Pasq104/SWDP-GeoGuesserProject/Report/img/ble_config2.png

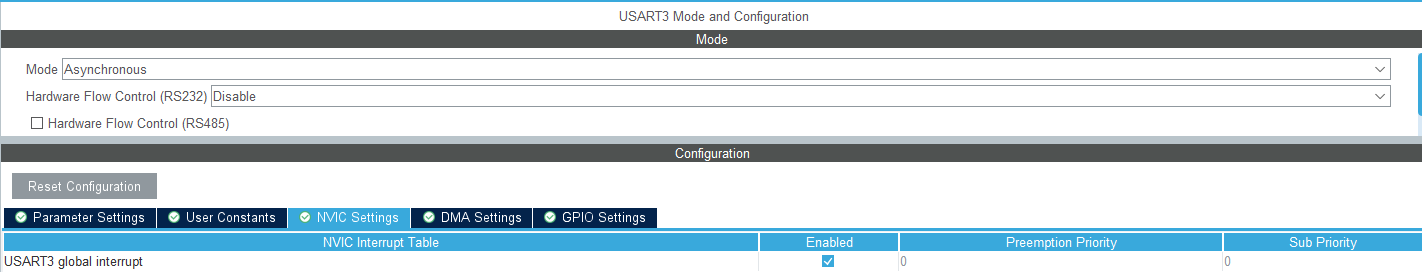
Report/img/ble_config2.png
