Pasq104/SWDP-GeoGuesserProject/Report/img/ble_config.png

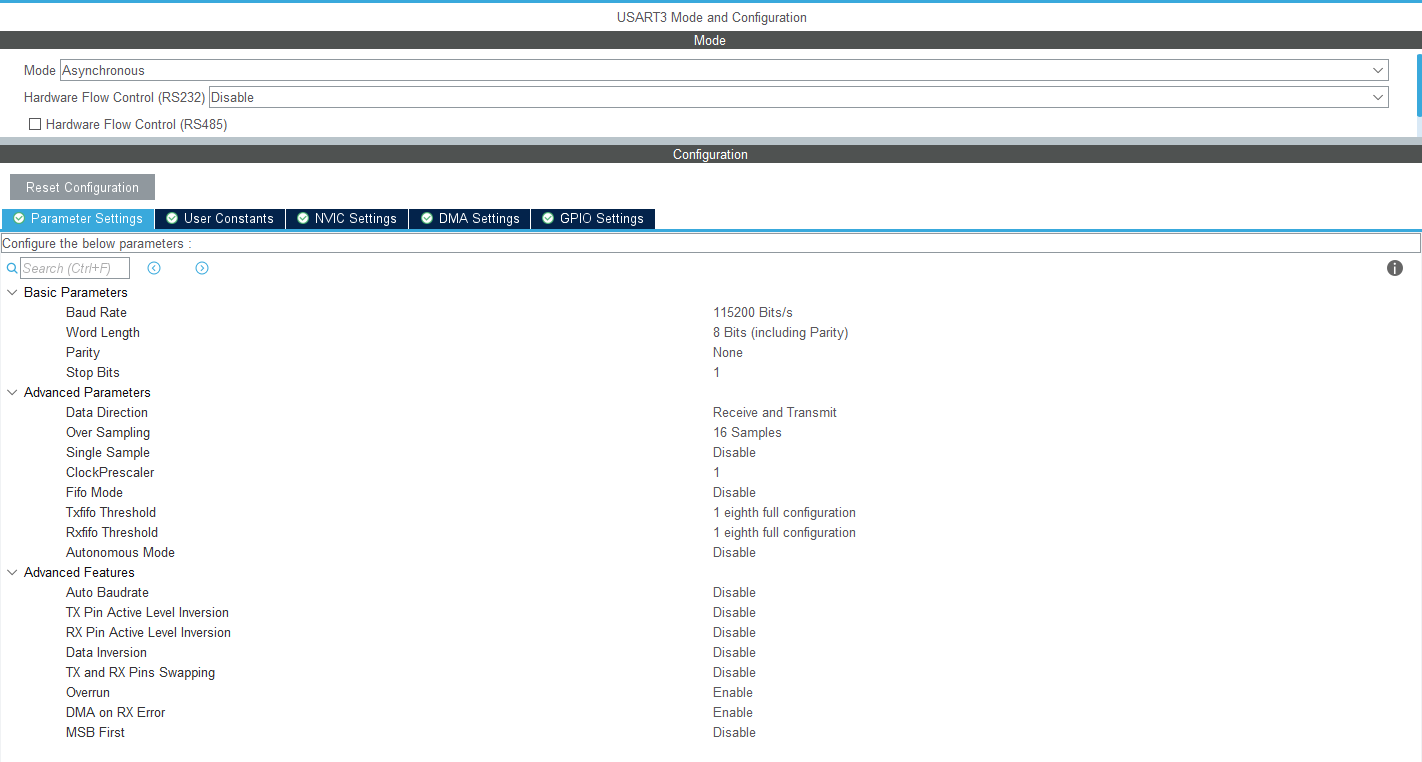
Report/img/ble_config.png
