Pasq104/SWDP-GeoGuesserProject/Report/img/connector.png

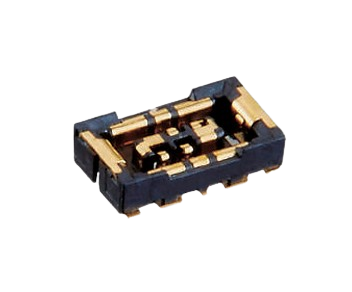
Report/img/connector.png
