Pasq104/SWDP-GeoGuesserProject/Report/img/finite_state_machine.png

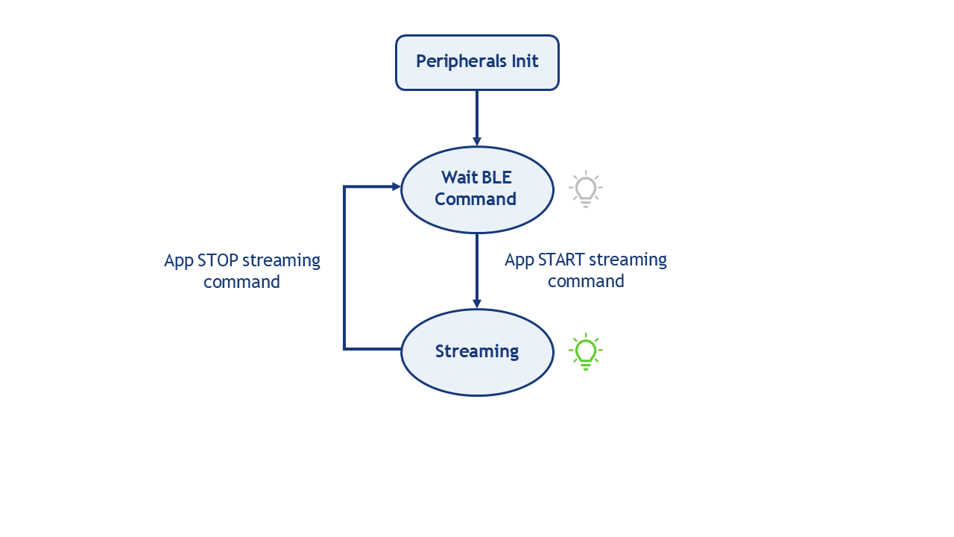
Report/img/finite_state_machine.png
