Pasq104/SWDP-GeoGuesserProject/Report/img/gyr_plot.png

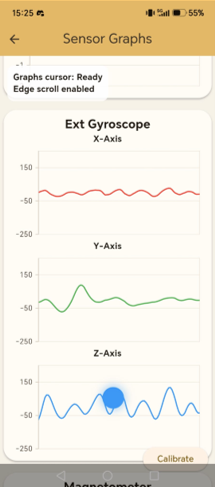
Report/img/gyr_plot.png
