Pasq104/SWDP-GeoGuesserProject/Report/img/Mag.png

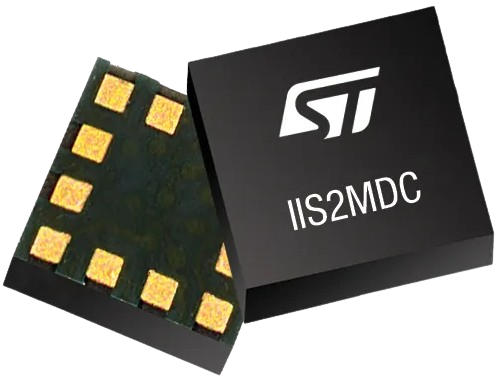
Report/img/Mag.png
