Pasq104/SWDP-GeoGuesserProject/Report/img/mcu_config.png

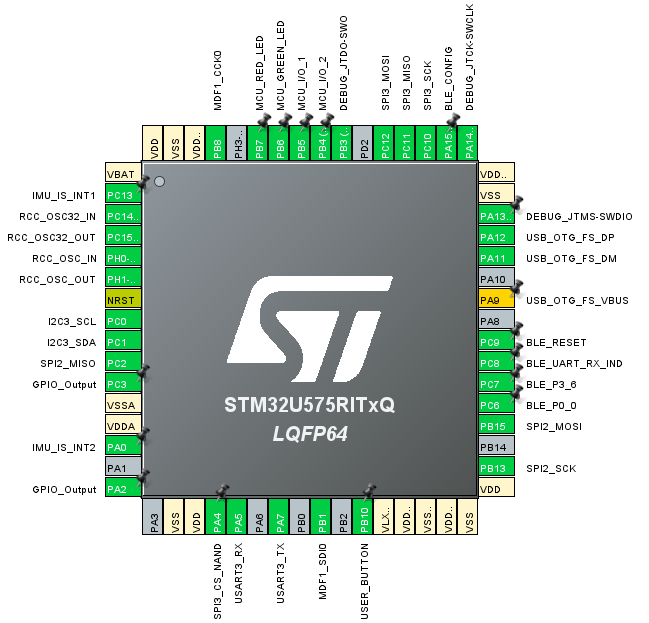
Report/img/mcu_config.png
