Pasq104/SWDP-GeoGuesserProject/Report/img/pcb_price.jpeg

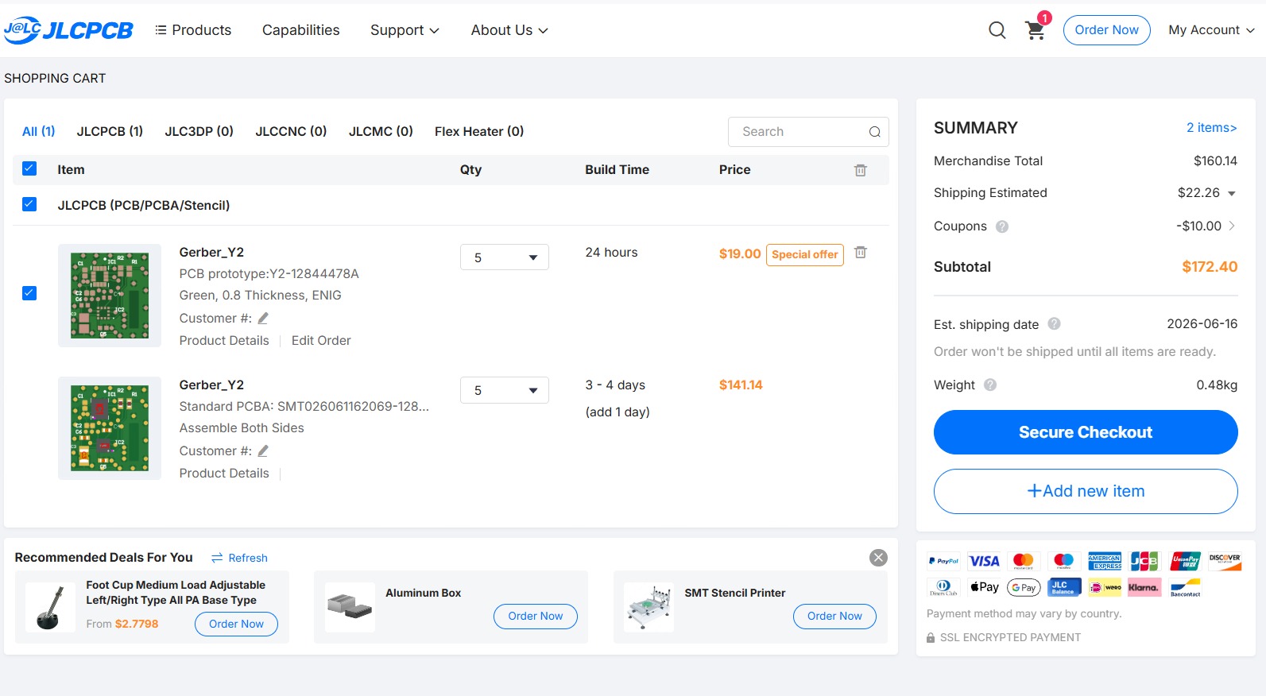
Report/img/pcb_price.jpeg
