Pasq104/SWDP-GeoGuesserProject/Report/img/spi_config.png

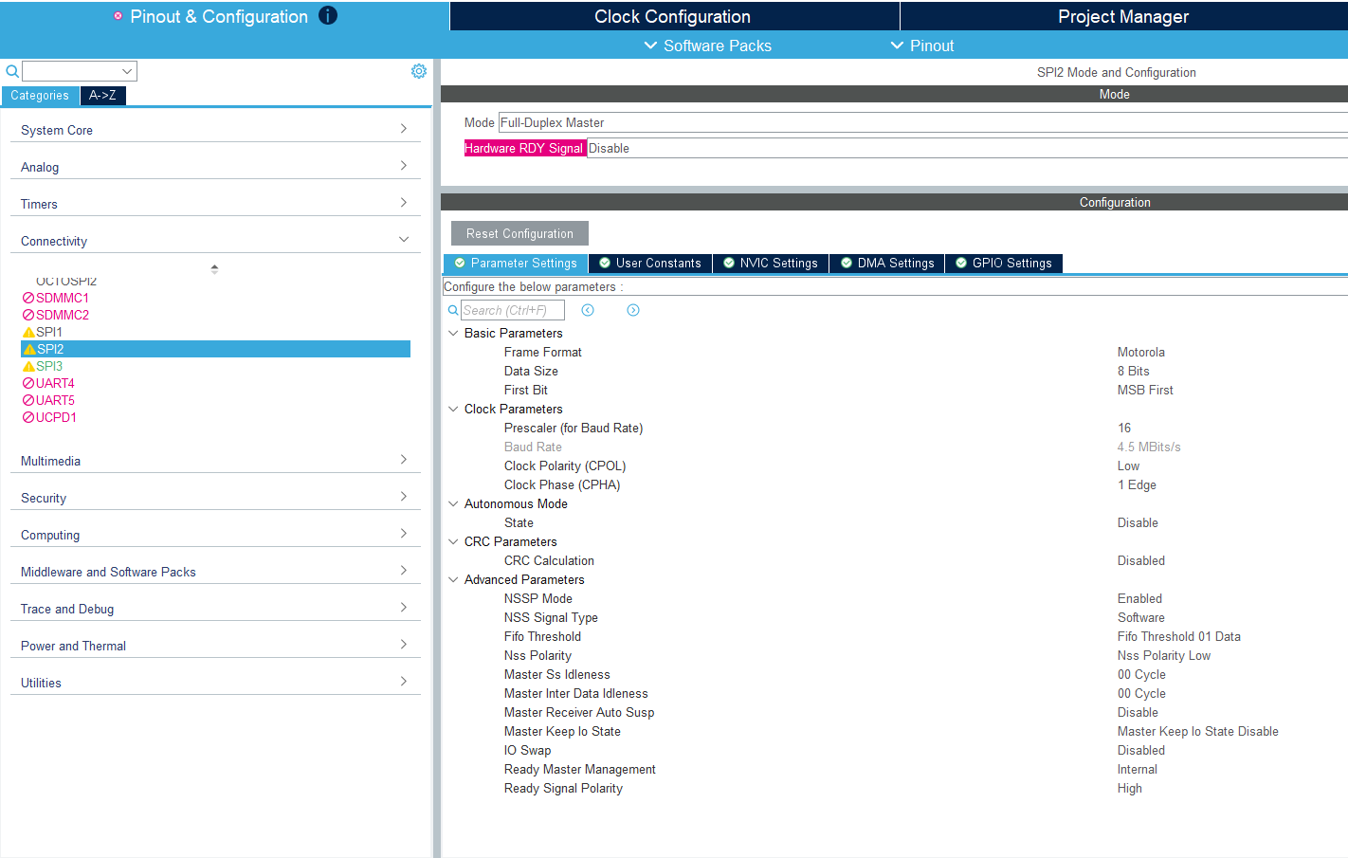
Report/img/spi_config.png
