Pasq104/SWDP-GeoGuesserProject/Report/img/stackup.png

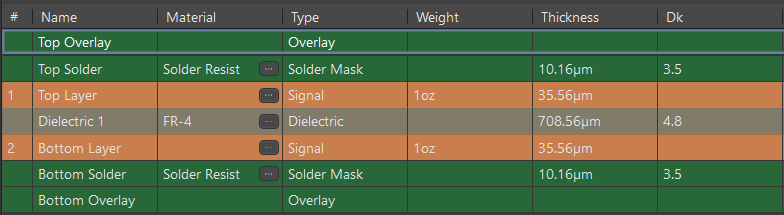
Report/img/stackup.png
