Pasq104/SWDP-GeoGuesserProject/Report/img/tim_config.png

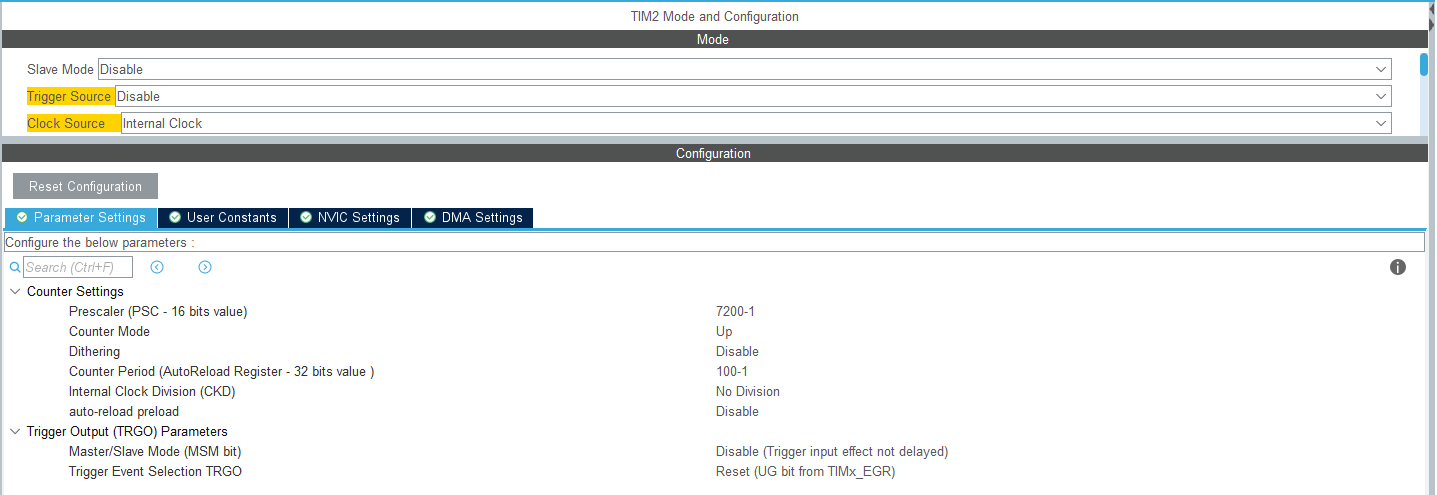
Report/img/tim_config.png
